AmmarSyamil/Rota_Pi/image/19.png

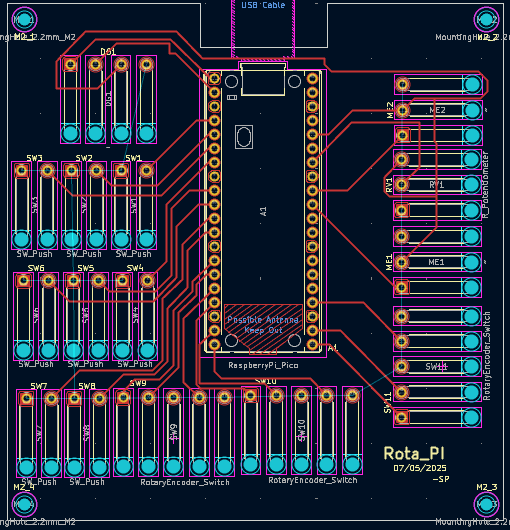
image/19.png
