AmmarSyamil/Rota_Pi/3D model/left part/front_cap_left.3mf

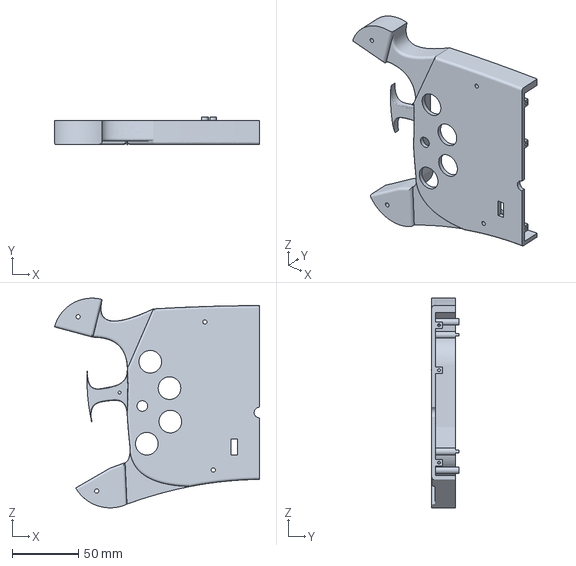
[picture p17: CAD file, 2025-07-15]
3D model/left part/front_cap_left.3mf
154.6 x 21.0 x 158.1 mm
