AmmarSyamil/Rota_Pi/3D model/clamp/clamp body.3mf

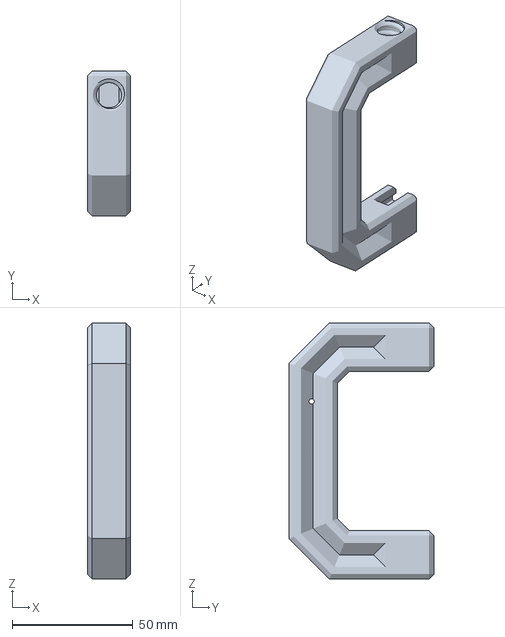
[picture p18: CAD file, 2025-07-15]
3D model/clamp/clamp body.3mf
18.0 x 60.0 x 106.0 mm
